argaar/BLEDeck/firmware/src/images.h

#define LOGO_IMAGE_WIDTH  72
#define LOGO_IMAGE_HEIGHT 58
static const unsigned char PROGMEM LOGO_IMAGE[] = {
 0x00,0x00,0x00,0x00,0x00,0x00,0x00,0x00,0x00,0x00,0x80,0x07,
 0x00,0x00,0x00,0x00,0x00,0x00,0x00,0xe0,0x07,0x00,0x00,0x00,
 0x00,0x00,0x00,0x00,0xf0,0x00,0x00,0x00,0x00,0x00,0x00,0x00,
 0x00,0x78,0x00,0x00,0x00,0x00,0x00,0x00,0x00,0x00,0x1c,0x1c,
 0x00,0x00,0x00,0x00,0x00,0x00,0x00,0x0c,0x1f,0x00,0x00,0x00,
 0x00,0x00,0x00,0x00,0x8e,0x07,0x00,0x00,0x00,0x00,0x00,0x00,
 0x00,0xc7,0x01,0x00,0x00,0x00,0x00,0x00,0x00,0x00,0xc7,0x00,
 0x00,0x00,0x00,0x00,0x00,0x00,0x00,0x63,0x20,0xa5,0xaa,0xaa,
 0xaa,0x02,0x00,0x00,0x63,0xfc,0xff,0xff,0xff,0xff,0x07,0x00,
 0x00,0x63,0xfe,0xfb,0xee,0xee,0xee,0x1e,0x00,0x00,0x00,0x06,
 0x00,0x00,0x00,0x00,0x1c,0x00,0x00,0x00,0x07,0x00,0x00,0x00,
 0x00,0x38,0x00,0x00,0x00,0x05,0x00,0x00,0x00,0x00,0x18,0x00,
 0x00,0x00,0xc3,0xe7,0xe3,0x03,0x7e,0x38,0x00,0x00,0x00,0xe7,
 0xe3,0xf3,0x01,0x7f,0x18,0x00,0x00,0x00,0xc3,0xe3,0xf3,0x83,
 0xdf,0x39,0x00,0x00,0x80,0xe3,0x72,0xe3,0xc0,0x9b,0x11,0x00,
 0x00,0x00,0xe3,0xe3,0xf1,0xc1,0xce,0x39,0x00,0x00,0x80,0x03,
 0x00,0x00,0xc0,0xef,0x19,0x00,0x00,0x80,0x01,0x00,0x00,0xc0,
 0x7f,0x39,0x00,0x00,0x80,0xa1,0xd0,0x50,0x40,0xfb,0x19,0x00,
 0x00,0x80,0xf1,0xf3,0xf9,0x81,0xdf,0x38,0x00,0x00,0xc0,0xd1,
 0xf1,0xf1,0x80,0xff,0x28,0x00,0x00,0x80,0xf1,0xb9,0xf8,0x00,
 0x36,0x38,0x00,0x00,0xc0,0x71,0xf1,0xb9,0x00,0x08,0x18,0x00,
 0x00,0xc0,0x80,0x00,0x40,0x00,0x00,0x38,0x00,0x00,0xc0,0x01,
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
 0x00, 0x00, 0x80, 0x03, 0x1c, 0x00, 0x00, 0x80,
 0x03, 0x1c, 0x00, 0x00, 0x80, 0x03, 0x3c, 0x00,
 0x00, 0xc0, 0x03, 0xfc, 0xff, 0xff, 0xff, 0x01,
 0xf8, 0xff, 0xff, 0xff, 0x01, 0xe0, 0xff, 0xff,
 0x7f, 0x00, 0x00, 0x00, 0x00, 0x00, 0x00, 0x00,
 0x00, 0x00, 0x00, 0x00};
